NCMST/Electrospinning-device/Hardware/Simulation/CCF1.asc

C1: cap; 0.466µ; V=3K Irms=0 Rser=0.0236 Lser=663p
C2: cap; 0.436µ; V=3K Irms=0 Rser=0.0236 Lser=663p
C3: cap; 0.445µ; V=3K Irms=0 Rser=0.0236 Lser=663p
C4: cap; 0.468µ; V=3K Irms=0 Rser=0.0236 Lser=663p
C5: cap; 0.460µ; V=3K Irms=0 Rser=0.0236 Lser=663p
C6: cap; 0.449µ; V=3K Irms=0 Rser=0.0236 Lser=663p
C7: cap; 0.434µ; V=3K Irms=0 Rser=0.0236 Lser=663p
C8: cap; 0.451µ; V=3K Irms=0 Rser=0.0236 Lser=663p
D1: diode; D_2CL77
D2: diode; D_2CL77
D3: diode; D_2CL77
D4: diode; D_2CL77
D5: diode; D_2CL77
D6: diode; D_2CL77
D7: diode; D_2CL77
D8: diode; D_2CL77
Lp: ind; 1.35; Ipk=6.9 Rser=3.1 Rpar=0 Cpar=0
Ls: ind; 56.2; Ipk=1.4 Rser=207.5 Rpar=16970 Cpar=1.698p
R1: res; 1
V1: voltage; SINE(0 150 50)
Named nets: 0, Out
K Lp Ls 1
.model D_2CL77 D(Is=1e-22 Rs=0.01 N=1 Cjo=10p BV=20000 IBV=0.005)
.tran 0 5 0
