NCMST/Electrospinning-device/Hardware/Simulation/HIGH_Voltage_Power_Supply.asc

C1: cap; 500n; V=3K Irms=0 Rser=0.1877 Lser=395p
C2: cap; 500n; V=3K Irms=0 Rser=0.1877 Lser=395p
C3: cap; 500n; V=3K Irms=0 Rser=0.1877 Lser=395p
C4: cap; 500n; V=3K Irms=0 Rser=0.1877 Lser=395p
C5: cap; 500n; V=3K Irms=0 Rser=0.1877 Lser=395p
C6: cap; 500n; V=3K Irms=0 Rser=0.1877 Lser=395p
C7: cap; 500n; V=3K Irms=0 Rser=0.1877 Lser=395p
C8: cap; 500n; V=3K Irms=0 Rser=0.1877 Lser=395p
C9: cap; 500n; V=3K Irms=0 Rser=0.1877 Lser=395p
D1: diode; D_2CL77
D2: diode; D_2CL77
D3: diode; D_2CL77
D4: diode; D_2CL77
D5: diode; D_2CL77
D6: diode; D_2CL77
D7: diode; D_2CL77
D8: diode; D_2CL77
D9: diode; D_2CL77
L1: ind2; 0.1
L2: ind2; 10
R1: res; 5000; tol=1 pwr=10
V1: voltage; SINE(0 150 50); AC 0; Rser=1 Cpar=0
Named nets: 0, Out, DC, Actual
.model D_2CL77 D (IS=1e-15 BV=20000 IBV=2uA CJO=2pF TT=80n)
K1 L1 L2 1
.tran 5
